MarcoAntonioGoncalves/Switch-Mode-Power-Supply-12-V-3-W/Hardware/3d View/SwitchModePowerSupply3dView.png

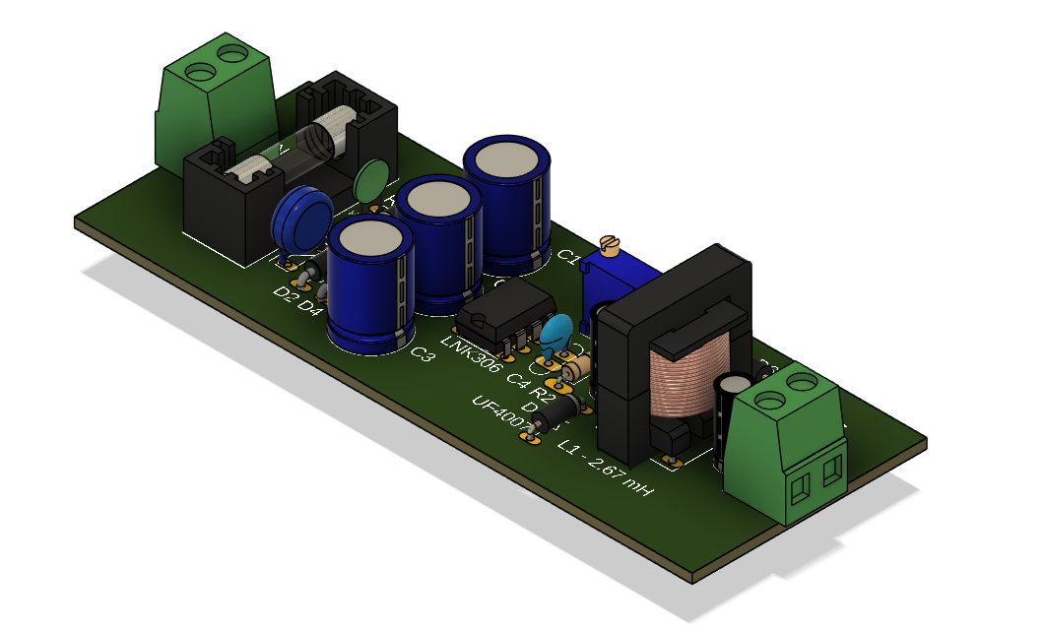
Hardware/3d View/SwitchModePowerSupply3dView.png
