MarcoAntonioGoncalves/Switch-Mode-Power-Supply-12-V-3-W/Hardware/PCB layout/SwitchModePowerSupplyBoard.png

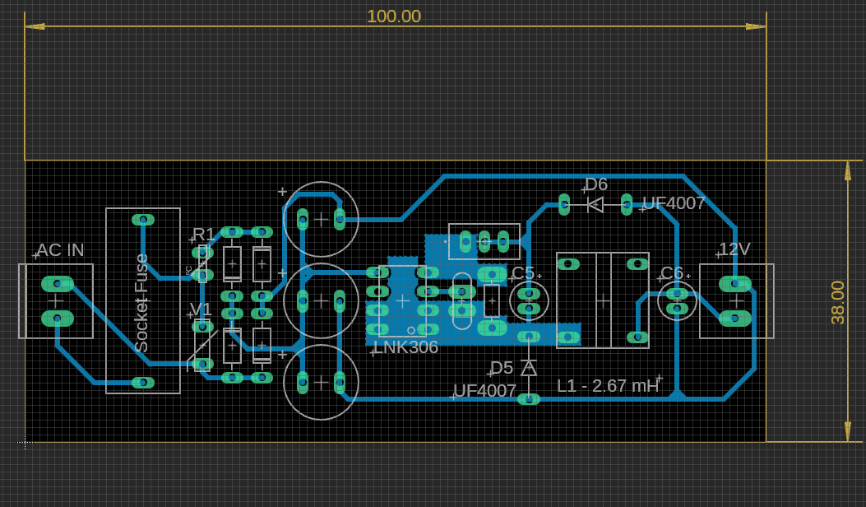
Hardware/PCB layout/SwitchModePowerSupplyBoard.png
