MarcoAntonioGoncalves/Switch-Mode-Power-Supply-12-V-3-W/Hardware/Schematic/SwitchModePowerSupplySch.png

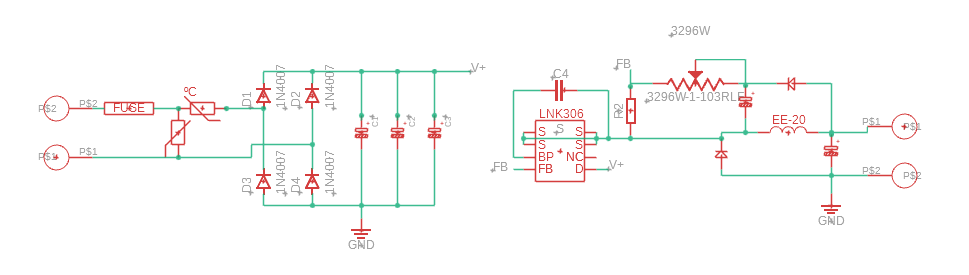
Hardware/Schematic/SwitchModePowerSupplySch.png
